kbx81/RGBBinaryClock/src/v1/Hardware.h

//
// kbx81's binary clock Hardware class
// ---------------------------------------------------------------------------
// (c)2017 by kbx81. See LICENSE for details.
//
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
#pragma once

#include <cstddef>
#include <cstdint>
#include "DateTime.h"
#include "Display.h"
#include "RgbLed.h"

#ifndef HARDWARE_VERSION
  #error HARDWARE_VERSION must be defined with a value between 1 and 4
#endif


namespace kbxBinaryClock {

namespace Hardware {

  /// @brief SPI1 peripherals
  ///
  enum SpiPeripheral : uint8_t {
    NotInitialized,
    LedDriversGs,
    LedDriversOther,
    Rtc,
    TempSensor
  };

  /// @brief Hardware request return codes
  ///
  enum HwReqAck : uint8_t {
    HwReqAckOk,
    HwReqAckBusy,
    HwReqAckError
  };


  /// @brief Hardware version to build for
  ///
  static const uint32_t cTargetHardwareVersion = HARDWARE_VERSION;


  /// @brief Initialize the hardware
  ///
  void     initialize();

  /// @brief Refreshes hardware external to the MCU
  ///
  void     refresh();

  /// @brief Generates a tick sound if no tone is active
  /// @return HwReqOk if tick was activated, HwReqBusy if tick was queued, else HwReqError
  HwReqAck tick();

  /// @brief Generates a tone of frequency for duration milliseconds
  /// @return HwReqOk if tone was activated, HwReqBusy if tone was queued, else HwReqError
  HwReqAck tone(const uint16_t frequency, const uint16_t duration);

  /// @brief Returns true if an external alarm input pin is active (they are active low)
  ///
  bool     alarmInput(const uint8_t alarmInputNumber);

  /// @brief Check a button
  ///
  bool     button(const uint8_t button);

  /// @brief Returns a bitmap indicating the state of all six buttons
  ///
  uint8_t  buttons();

  /// @brief Returns a bitmap indicating buttons that were pressed since the last check
  ///
  uint8_t  buttonsPressed();

  /// @brief Returns a bitmap indicating buttons that were released since the last check
  ///
  uint8_t  buttonsReleased();

  /// @brief Refreshes the button states from the TSC
  ///
  void     buttonsRefresh();

  /// @brief Set the current drive level for the drivers
  ///
  void     setLedCurrentDrive(const uint8_t drive);

  /// @brief Enable or disable the display blanking output pin
  ///
  void     setDisplayHardwareBlanking(const bool blankingState);

  /// @brief Returns the state of daylight savings time in hardware
  ///
  bool     dstState();

  /// @brief Get the current date/time
  ///
  DateTime getDateTime();

  /// @brief Set the date/time
  ///
  void     setDateTime(const DateTime &dateTime);

  /// @brief Returns the state of the RTC (true if year != 0)
  ///
  bool     rtcIsSet();

  /// @brief Returns the temperature based on hardware
  ///  (in fahrenheit if fahrenheit == true; in BCD if bcd == true)
  int32_t  temperature(const bool fahrenheit, const bool bcd);

  /// @brief Returns the level of light seen by the phototransistor (0 = min, 4095 = max)
  ///
  uint16_t lightLevel();

  /// @brief Adjusts the clock for daylight savings
  ///
  void     setDstState(const bool enableDst, const bool adjustRtcHardware);

  /// @brief Sets the value used as a threshold for flicker reduction at low intensities
  ///
  void     setFlickerReduction(const uint16_t value);

  /// @brief Sets the calibration value used for the temperature calculation
  ///
  void     setTemperatureCalibration(const int8_t value);

  /// @brief Sets the volume of tones emitted from the buzzer
  ///  Valid range is 0 (muted/minimum) to 7 (maximum/default)
  void     setVolume(const uint8_t volumeLevel);

  /// @brief Returns a CRC for the given data; expects 32-bit words
  ///
  uint32_t getCRC(uint32_t *inputData, uint32_t numElements);

  /// @brief Erases the FLASH area used for app data
  /// @return 0xff if startAddress is out of range, flash_get_status_flags() if
  ///  erase request failed, 0x40 if erase verification failed
  uint32_t eraseFlash(uint32_t startAddress);

  /// @brief Reads the FLASH area used for app data
  ///
  void     readFlash(uint32_t startAddress, uint16_t numElements, uint8_t *outputData);

  /// @brief Writes the FLASH area used for app data
  /// @return 0xff if startAddress is out of range, flash_get_status_flags() if
  ///  erase request failed, 0x40 if erase verification failed,
  ///  (0x80 | flash_get_status_flags()) if programming failure
  uint32_t writeFlash(uint32_t startAddress, uint8_t *inputData, uint16_t numElements);

  /// @brief Reads and/or writes data to/from specified I2C interface via DMA
  ///
  HwReqAck i2cTransfer(const uint8_t addr, const uint8_t *bufferTx, size_t numberTx, uint8_t *bufferRx, size_t numberRx);

  /// @brief Reads and/or writes data to/from the I2C1 interface via DMA
  ///
  HwReqAck i2cReceive(const uint8_t addr, uint8_t *bufferRx, const size_t numberRx, const bool autoEndXfer);
  HwReqAck i2cTransmit(const uint8_t addr, const uint8_t *bufferTx, const size_t numberTx, const bool autoEndXfer);

  /// @brief Aborts a transfer initiated by i2cTransfer()
  ///
  void     i2cAbort();

  /// @brief Permits checking the status of the I2C; returns true if busy
  ///
  bool     i2cIsBusy();

  /// @brief Reads data from the serial port with DMA
  /// @return false if failure (the USART was busy)
  HwReqAck readSerial(const uint32_t usart, const uint32_t length, char* data);

  /// @brief Writes data to the serial port with DMA
  /// @return false if failure (the USART was busy)
  HwReqAck writeSerial(const uint32_t usart, const uint32_t length, const char* data);

  /// @brief Transfers data in/out through the SPI via DMA
  /// @return false if failure (the SPI was busy)
  HwReqAck spiTransfer(const SpiPeripheral peripheral, uint8_t *bufferIn, uint8_t *bufferOut, const uint16_t length, const bool use16BitXfers);

  /// @brief Permits checking the status of the SPI; returns true if busy
  ///
  bool     spiIsBusy();

  /// @brief Sets the given status LED to the given intensity/RgbLed
  ///
  void     setBlueLed(const uint32_t intensity);
  void     setGreenLed(const uint32_t intensity);
  void     setRedLed(const uint32_t intensity);
  void     setStatusLed(const RgbLed led);
  void     blinkStatusLed(const RgbLed led1, const RgbLed led2, uint32_t numberOfBlinks, const uint32_t delayLength);

  /// @brief Creates a delay of length based on systick (configured for milliseconds)
  ///
  void     delay(const uint32_t length);

  /// @brief Converts to/from int/BCD
  /// @return encoded value
  ///
  uint32_t bcdToUint32(uint32_t bcdValue);
  uint32_t uint32ToBcd(uint32_t uint32Value); // beware of values > 99999999


  /// @brief Interrupt Service Routines
  ///
  void     dmaIsr();
  void     systickIsr();
  void     tim2Isr();
  void     tim15Isr();
  void     tim16Isr();
  void     tscIsr();
  void     usart1Isr();
  void     usart2Isr();

}

}
