kbx81/RGBBinaryClock/src/v1/Application.cpp

//
// kbx81's binary clock main application
// ---------------------------------------------------------------------------
// (c)2017 by kbx81. See LICENSE for details.
//
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
#include <cstdint>

#include "Application.h"
#include "AlarmHandler.h"
#include "DateTime.h"
#include "Display.h"
#include "DisplayManager.h"
#include "Dmx-512-Controller.h"
#include "Dmx-512-Rx.h"
#include "Dmx-512-View.h"
#include "Keys.h"
#include "Settings.h"
#include "MainMenuView.h"
#include "TestDisplayView.h"
#include "TimeDateTempView.h"
#include "TimerCounterView.h"
#include "SetTimeDateView.h"
#include "SetValueView.h"
#include "SetBitsView.h"
#include "SetColorsView.h"


// Workaround for  "hidden symbol `__dso_handle' isn't defined" linker error
void* __dso_handle;


namespace kbxBinaryClock {

namespace Application {


// An array with all views for the application
//
static View* const cModeViews[] = {
    new MainMenuView(),
    new TimeDateTempView(),
    new TimerCounterView(),
    new Dmx512View(),
    new SetTimeDateView(),
    new SetBitsView(),
    new SetValueView(),
    new SetColorsView(),
    new TestDisplayView()
};

// Structure defining menu views
//
struct viewDescriptor {
  uint8_t  menuItemDisplayNumber;
  ViewEnum view;
  uint8_t  relatedSettingNumber;
};


// An array of mode display numbers and their corresponding views
//
static viewDescriptor const cViewDescriptor[] = {
    {  0, ViewEnum::MainMenuViewEnum,     Settings::Setting::SystemOptions }, // OperatingModeMainMenu
    {  1, ViewEnum::TimeDateTempViewEnum, Settings::Setting::SystemOptions }, // OperatingModeFixedDisplay
    {  2, ViewEnum::TimeDateTempViewEnum, Settings::Setting::SystemOptions }, // OperatingModeToggleDisplay
    {  3, ViewEnum::TimerCounterViewEnum, Settings::Setting::SystemOptions }, // OperatingModeTimerCounter
    {  4, ViewEnum::Dmx512ViewEnum,       Settings::Setting::SystemOptions }, // OperatingModeDmx512Display
    {  5, ViewEnum::SetTimeDateViewEnum,  Settings::Setting::SystemOptions }, // OperatingModeSetClock
    {  6, ViewEnum::SetTimeDateViewEnum,  Settings::Setting::SystemOptions }, // OperatingModeSetDate
    {  7, ViewEnum::SetValueViewEnum,     Settings::Setting::TimerResetValue },
    { 10, ViewEnum::SetBitsViewEnum,      Settings::Setting::SystemOptions },
    { 11, ViewEnum::SetBitsViewEnum,      Settings::Setting::BeepStates },
    { 12, ViewEnum::SetBitsViewEnum,      Settings::Setting::BlinkStates },
    { 13, ViewEnum::SetBitsViewEnum,      Settings::Setting::ColorStates },
    { 20, ViewEnum::SetValueViewEnum,     Settings::Setting::TimeDisplayDuration },
    { 21, ViewEnum::SetValueViewEnum,     Settings::Setting::DateDisplayDuration },
    { 22, ViewEnum::SetValueViewEnum,     Settings::Setting::TemperatureDisplayDuration },
    { 23, ViewEnum::SetValueViewEnum,     Settings::Setting::FadeDuration },
    { 24, ViewEnum::SetValueViewEnum,     Settings::Setting::DstBeginMonth },
    { 25, ViewEnum::SetValueViewEnum,     Settings::Setting::DstBeginDowOrdinal },
    { 26, ViewEnum::SetValueViewEnum,     Settings::Setting::DstEndMonth },
    { 27, ViewEnum::SetValueViewEnum,     Settings::Setting::DstEndDowOrdinal },
    { 28, ViewEnum::SetValueViewEnum,     Settings::Setting::DstSwitchDayOfWeek },
    { 29, ViewEnum::SetValueViewEnum,     Settings::Setting::DstSwitchHour },
    { 30, ViewEnum::SetValueViewEnum,     Settings::Setting::MinimumIntensity },
    { 31, ViewEnum::SetValueViewEnum,     Settings::Setting::FlickerReduction },
    { 32, ViewEnum::SetValueViewEnum,     Settings::Setting::CurrentDrive },
    { 33, ViewEnum::SetValueViewEnum,     Settings::Setting::TemperatureCalibration },
    { 34, ViewEnum::SetValueViewEnum,     Settings::Setting::BeeperVolume },
    { 35, ViewEnum::SetValueViewEnum,     Settings::Setting::DateFormat },
    { 36, ViewEnum::SetValueViewEnum,     Settings::Setting::DisplayRefreshInterval },
    { 39, ViewEnum::SetValueViewEnum,     Settings::Setting::DmxAddress },
    { 40, ViewEnum::SetTimeDateViewEnum,  Settings::Slot::Slot1 },
    { 41, ViewEnum::SetTimeDateViewEnum,  Settings::Slot::Slot2 },
    { 42, ViewEnum::SetTimeDateViewEnum,  Settings::Slot::Slot3 },
    { 43, ViewEnum::SetTimeDateViewEnum,  Settings::Slot::Slot4 },
    { 44, ViewEnum::SetTimeDateViewEnum,  Settings::Slot::Slot5 },
    { 45, ViewEnum::SetTimeDateViewEnum,  Settings::Slot::Slot6 },
    { 46, ViewEnum::SetTimeDateViewEnum,  Settings::Slot::Slot7 },
    { 47, ViewEnum::SetTimeDateViewEnum,  Settings::Slot::Slot8 },
    { 50, ViewEnum::SetColorsViewEnum,    Settings::Slot::Slot1 },
    { 51, ViewEnum::SetColorsViewEnum,    Settings::Slot::Slot2 },
    { 52, ViewEnum::SetColorsViewEnum,    Settings::Slot::Slot3 },
    { 53, ViewEnum::SetColorsViewEnum,    Settings::Slot::Slot4 },
    { 54, ViewEnum::SetColorsViewEnum,    Settings::Slot::Slot5 },
    { 55, ViewEnum::SetColorsViewEnum,    Settings::Slot::Slot6 },
    { 56, ViewEnum::SetColorsViewEnum,    Settings::Slot::Slot7 },
    { 57, ViewEnum::SetColorsViewEnum,    Settings::Slot::Slot8 },
    { 58, ViewEnum::SetColorsViewEnum,    Settings::Slot::SlotDate },
    { 59, ViewEnum::SetColorsViewEnum,    Settings::Slot::SlotTemperature },
    { 60, ViewEnum::SetColorsViewEnum,    Settings::Slot::SlotTimer },
    { 61, ViewEnum::SetColorsViewEnum,    Settings::Slot::SlotMenu },
    { 62, ViewEnum::SetColorsViewEnum,    Settings::Slot::SlotSet },
    { 98, ViewEnum::TestDisplayEnum,      Settings::Setting::SystemOptions }
};

// The maximum idle time before the application switches back to the default view
//   Counter is incremented by tick()
static const uint16_t cMaximumIdleCount = 60000;

// A value by which we multiply the preference stored in the Settings
//
static const uint8_t cMinimumIntensityMultiplier = 10;

// Idle cycle counter
//
volatile static uint16_t _idleCounter = cMaximumIdleCount;

// minimum intensity
//   100 = 1%
static uint16_t _minimumIntensity = cMinimumIntensityMultiplier;

// master display intensity
//
static uint16_t _intensityPercentage = _minimumIntensity;

// important daylight savings dates & times
//
static DateTime _currentTime, _dstStart, _dstEnd;

// daylight savings state
//
static DstState _dstState;

// The current mode of the application
//
static OperatingMode _applicationMode;

// The application's current view mode
//
static ViewMode _viewMode;

// The application's current external control mode
//
static ExternalControl _externalControlMode = ExternalControl::NoActiveExtControlEnum;

// The application's current settings
//
static Settings _settings;

// The current displayed view of the application
//
// View *_currentView = cModeViews[static_cast<uint8_t>(OperatingMode::OperatingModeFixedDisplay)];
static View *_currentView = cModeViews[static_cast<uint8_t>(ViewEnum::TimeDateTempViewEnum)];

// determines if display intensity is adjusted in real-time
//
static bool _autoAdjustIntensities = false;

// DMX-512 signal status the last time we checked
//
static bool _previousDmxState = false;

// True if settings need to be written to FLASH
//
static bool _settingsModified = false;


void initialize()
{
  if (_settings.loadFromFlash() == false)
  {
    // blink to alert that settings could not be loaded
    Hardware::blinkStatusLed(Application::green, Application::orange, 12, 80);
    Hardware::delay(500);
    Hardware::setStatusLed(RgbLed());
  }

  _currentTime = Hardware::getDateTime();
  // Update DST start and end dates and times based on RTC
  isDst(_currentTime);

  AlarmHandler::initialize();

  Dmx512Controller::initialize();
  // setOperatingMode() will refreshSettings()
  if (_settings.getSetting(Settings::Setting::SystemOptions, Settings::SystemOptionsBits::StartupToToggle) == true)
  {
    setOperatingMode(OperatingMode::OperatingModeToggleDisplay);
  }
  else
  {
    setOperatingMode(OperatingMode::OperatingModeFixedDisplay);
  }
}


uint8_t getModeDisplayNumber(OperatingMode mode)
{
  return cViewDescriptor[static_cast<uint8_t>(mode)].menuItemDisplayNumber;
}


uint8_t getModeDisplayNumber(uint8_t mode)
{
  if (mode <= static_cast<uint8_t>(OperatingMode::OperatingModeTestDisplay))
  {
    return cViewDescriptor[mode].menuItemDisplayNumber;
  }
  return 0;
}


OperatingMode getOperatingMode()
{
  return _applicationMode;
}


void setOperatingMode(OperatingMode mode)
{
  if (_applicationMode != mode)
  {
    const uint16_t writeLedIntensity = 1024;
    // first, write settings to FLASH, if needed
    if ((mode != OperatingMode::OperatingModeMainMenu) &&
        (mode < static_cast<uint8_t>(OperatingMode::OperatingModeSetSystemOptions)) &&
        (_settingsModified == true))
    {
      if (_settings.saveToFlash() == 0)
      {
        _settingsModified = false;
        Hardware::setGreenLed(writeLedIntensity);
      }
      else
      {
        Hardware::setRedLed(writeLedIntensity);
      }
      DisplayManager::doubleBlink();
      Hardware::setStatusLed(RgbLed());
    }
    // ensure hardware is consistent with current settings
    refreshSettings();
    // set the new mode
    _applicationMode = mode;
    _viewMode = ViewMode::ViewMode0;
    _currentView = cModeViews[static_cast<uint8_t>(cViewDescriptor[static_cast<uint8_t>(mode)].view)];
    _currentView->enter();
    // if something kicks back to the main menu, make sure we wait a full cycle
    if (mode == OperatingMode::OperatingModeMainMenu)
    {
      _idleCounter = 0;
    }
    // this enables controller() immediately upon entering this mode
    else if (mode == OperatingMode::OperatingModeDmx512Display)
    {
      _idleCounter = cMaximumIdleCount;
    }
  }
}


ViewMode getViewMode()
{
  return _viewMode;
}


void setViewMode(ViewMode mode)
{
  if (_viewMode != mode)
  {
    _viewMode = mode;
  }
}


uint8_t getOperatingModeRelatedSetting(OperatingMode mode)
{
  return cViewDescriptor[static_cast<uint8_t>(mode)].relatedSettingNumber;
}


ExternalControl getExternalControlState()
{
  return _externalControlMode;
}


Settings getSettings()
{
  return _settings;
}


Settings* getSettingsPtr()
{
  return &_settings;
}


void refreshSettings()
{
  // Update hardware things
  Hardware::setFlickerReduction(_settings.getRawSetting(Settings::Setting::FlickerReduction));
  Hardware::setVolume(_settings.getRawSetting(Settings::Setting::BeeperVolume));
  Hardware::setLedCurrentDrive(_settings.getRawSetting(Settings::Setting::CurrentDrive));
  Hardware::setTemperatureCalibration((int8_t)(-(_settings.getRawSetting(Settings::Setting::TemperatureCalibration))));

  DisplayManager::setDisplayRefreshInterval(_settings.getRawSetting(Settings::Setting::DisplayRefreshInterval));
  DisplayManager::setDisplayBlanking(false);

  _minimumIntensity = _settings.getRawSetting(Settings::Setting::MinimumIntensity) * cMinimumIntensityMultiplier;
  setIntensityAutoAdjust(_settings.getSetting(Settings::Setting::SystemOptions, Settings::SystemOptionsBits::AutoAdjustIntensity), true);
}


void setSettings(Settings settings)
{
  _settings = settings;

  refreshSettings();

  _settingsModified = true;
}


// Handles DST date/time computation and setup
//
bool isDst(const DateTime &currentTime)
{
  uint8_t firstDay;

  if (_dstStart.year(false) != currentTime.year(false))
  {
    _dstState = DstState::Reset;
    firstDay = ((_settings.getRawSetting(Settings::Setting::DstBeginDowOrdinal) - 1) * 7) + 1;

    do
    {
      _dstStart.setDate(currentTime.year(false), _settings.getRawSetting(Settings::Setting::DstBeginMonth), firstDay++);
    }
    while((_dstStart.dayOfWeek() != _settings.getRawSetting(Settings::Setting::DstSwitchDayOfWeek)) && (firstDay <= 31));

    _dstStart.setTime(_settings.getRawSetting(Settings::Setting::DstSwitchHour), 0, 0);

    if (currentTime >= _dstStart)
    {
      _dstState = DstState::Spring;
    }
  }

  if (_dstEnd.year(false) != currentTime.year(false))
  {
    firstDay = ((_settings.getRawSetting(Settings::Setting::DstEndDowOrdinal) - 1) * 7) + 1;

    do
    {
      _dstEnd.setDate(currentTime.year(false), _settings.getRawSetting(Settings::Setting::DstEndMonth), firstDay++);
    }
    while((_dstEnd.dayOfWeek() != _settings.getRawSetting(Settings::Setting::DstSwitchDayOfWeek)) && (firstDay <= 31));

    _dstEnd.setTime(_settings.getRawSetting(Settings::Setting::DstSwitchHour), 0, 0);

    if (currentTime >= _dstEnd)
    {
      _dstState = DstState::Fall;
    }
  }

  // once everything is calculated above, it becomes this simple...
  return (currentTime >= _dstStart && currentTime < _dstEnd);
}


// Handles updating of the clock hardware for DST
//
void _refreshDst()
{
  _currentTime = Hardware::getDateTime();

  if ((_currentTime >= _dstEnd) && (_dstState == DstState::Spring))
  {
    _dstState = DstState::Fall;
    Hardware::setDstState(isDst(_currentTime), true);
  }

  if ((_currentTime >= _dstStart) && (_dstState == DstState::Reset))
  {
    _dstState = DstState::Spring;
    Hardware::setDstState(isDst(_currentTime), true);
  }
}


// Updates the "master" intensity for the display based on lightLevel()
//
void _updateIntensityPercentage(const bool quick = false)
{
  // determine the new value for _intensityPercentage
  uint16_t currentPercentage = (Hardware::lightLevel() * RgbLed::cLed100Percent) / Display::cLedMaxIntensity;

  // make sure the intensity does not go below the minimum level
  if (currentPercentage < _minimumIntensity)
  {
    currentPercentage = _minimumIntensity;
  }

  if (quick == true)
  {
    _intensityPercentage = currentPercentage;
  }
  else
  {
    if (currentPercentage > _intensityPercentage)
    {
     _intensityPercentage++;
    }
    else if (currentPercentage < _intensityPercentage)
    {
     _intensityPercentage--;
    }
  }
}


bool getIntensityAutoAdjust()
{
  return _autoAdjustIntensities;
}


void setIntensityAutoAdjust(const bool enable, const bool quickAdjust)
{
  if (_autoAdjustIntensities != enable)
  {
    _autoAdjustIntensities = enable;

    if ((enable == true) && (quickAdjust == true))
    {
      _updateIntensityPercentage(quickAdjust);
    }
  }
}


uint16_t getIntensity()
{
  return _intensityPercentage;
}


void setIntensity(const uint16_t intensity)
{
  _autoAdjustIntensities = false;

  if (intensity < RgbLed::cLed100Percent)
  {
    _intensityPercentage = intensity;
  }
  else
  {
    _intensityPercentage = RgbLed::cLed100Percent;
  }
}


void tick()
{
  if (_idleCounter <= cMaximumIdleCount)
  {
    _idleCounter++;
  }

  if (_autoAdjustIntensities == true)
  {
    _updateIntensityPercentage();
  }
}


// Here lies the main application loop
//
void loop()
{
  while(true)
  {
    // Refresh hardware data (date, time, temperature, etc.)
    Hardware::refresh();

    // Check up on DST and adjust the time if enabled based on settings
    if (_settings.getSetting(Settings::Setting::SystemOptions, Settings::SystemOptionsBits::DstEnable) == true)
    {
      _refreshDst();
    }
    // We control the master display intensity only if DMX-512 is NOT active
    if (_externalControlMode != ExternalControl::Dmx512ExtControlEnum)
    {
      DisplayManager::setMasterIntensity(_intensityPercentage);
    }

    // Check the buttons
    Keys::scanKeys();
    if (Keys::hasKeyPress())
    {
      // Get the key from the buffer and process it
      auto key = Keys::getKeyPress();
      // Reset the counter since there has been button/key activity
      _idleCounter = 0;
      // If an alarm is active and external control is not, send keypresses there
      if ((AlarmHandler::isAlarmActive())
       && (_externalControlMode == Application::ExternalControl::NoActiveExtControlEnum))
      {
        AlarmHandler::keyHandler(key);
      }
      else
      {
        if (_currentView->keyHandler(key) == true)
        {
          // The key did something, so make the tick sound
          Hardware::tick();
          // Take control back
          _externalControlMode = ExternalControl::NoActiveExtControlEnum;
          // Make sure the display is visible
          DisplayManager::setDisplayBlanking(false);
        }
      }
    }
    // Execute the loop block of the current view
    _currentView->loop();
    // We do not signal alarms if some external control is active
    if (_externalControlMode == Application::ExternalControl::NoActiveExtControlEnum)
    {
      // Process any necessary alarms
      AlarmHandler::loop();
    }

    // If the idle counter has maxed out, kick back to the appropriate display mode
    if (_idleCounter >= cMaximumIdleCount)
    {
      // If there is an active signal, update _externalControlMode
      if (Dmx512Rx::signalIsActive() == true)
      {
        _externalControlMode = ExternalControl::Dmx512ExtControlEnum;
      }
      // Kick back to the default display mode
      else if (_externalControlMode == ExternalControl::NoActiveExtControlEnum)
      {
        // Only change the display mode if it isn't already one of the time/date/temp modes
        if ((_applicationMode != OperatingMode::OperatingModeToggleDisplay) &&
            (_applicationMode != OperatingMode::OperatingModeFixedDisplay) &&
            (_applicationMode != OperatingMode::OperatingModeTimerCounter))
        {
          if (_settings.getSetting(Settings::Setting::SystemOptions, Settings::SystemOptionsBits::StartupToToggle) == true)
          {
            setOperatingMode(OperatingMode::OperatingModeToggleDisplay);
          }
          else
          {
            setOperatingMode(OperatingMode::OperatingModeFixedDisplay);
          }
        }
      }
    }

    if (_externalControlMode == ExternalControl::Dmx512ExtControlEnum)
    {
      // Allow the DMX-512 controller to do its thing
      Dmx512Controller::controller();
    }

    // Deal with changes in the DMX-512 signal state
    if (Dmx512Rx::signalIsActive() != _previousDmxState)
    {
      _previousDmxState = Dmx512Rx::signalIsActive();

      if (_previousDmxState == true)
      {
        _externalControlMode = ExternalControl::Dmx512ExtControlEnum;
      }
      else
      {
        _externalControlMode = ExternalControl::NoActiveExtControlEnum;
        AlarmHandler::clearAlarm();   // just in case...
      }
      // Setting this mode activates the view but also kicks us back to the menu if there is no signal
      setOperatingMode(OperatingMode::OperatingModeDmx512Display);
    }
  }
}


}

}
