kbx81/RGBBinaryClock/src/v1/MainMenuView.cpp

//
// kbx81's binary clock MainMenuView class
// ---------------------------------------------------------------------------
// (c)2017 by kbx81. See LICENSE for details.
//
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
#include "Application.h"
#include "DateTime.h"
#include "DisplayManager.h"
#include "MainMenuView.h"
#include "Settings.h"


namespace kbxBinaryClock {


MainMenuView::MainMenuView()
  : _selectedMode(0),
    _previousMode(0)
{
}


void MainMenuView::enter()
{
  // correct the mode if it's out of range
  if ((_selectedMode == 0) || (_selectedMode > Application::OperatingMode::OperatingModeSetColors))
  {
    _selectedMode = Application::OperatingMode::OperatingModeFixedDisplay;
  }
  // if the clock is not set, select the SetClock mode automagically
  if (Hardware::rtcIsSet() == false)
  {
    _selectedMode = Application::OperatingMode::OperatingModeSetClock;
  }
  // if the clock is set but not the date, select the SetDate mode automagically
  else if (Hardware::getDateTime().yearShort(false) == 0)
  {
    _selectedMode = Application::OperatingMode::OperatingModeSetDate;
  }

  DisplayManager::setStatusLedAutoRefreshing(false);
  // Make sure the status LEDs are off
  Hardware::setStatusLed(RgbLed());
}


bool MainMenuView::keyHandler(Keys::Key key)
{
  bool tick = true;

  if ((key == Keys::Key::A) &&
      (_selectedMode == static_cast<uint8_t>(Application::OperatingMode::OperatingModeTestDisplay) + 1))
  {
    Hardware::setStatusLed(Application::red);

    Hardware::eraseFlash(Settings::cSettingsFlashAddress);
    _selectedMode = 1;

    DisplayManager::doubleBlink();
    DisplayManager::doubleBlink();
    Hardware::setStatusLed(RgbLed());
  }

  if (key == Keys::Key::B)
  {
    Application::setOperatingMode(Application::OperatingMode::OperatingModeFixedDisplay);
  }

  if (key == Keys::Key::C)
  {
    Application::setOperatingMode(Application::OperatingMode::OperatingModeToggleDisplay);
  }

  if (key == Keys::Key::D)
  {
    if (--_selectedMode == 0)
    {
      _selectedMode = 1;

      tick = false;
    }
  }

  if (key == Keys::Key::U)
  {
    _selectedMode++;

    if (_selectedMode > static_cast<uint8_t>(Application::OperatingMode::OperatingModeTestDisplay) + 1)
    {
      _selectedMode = static_cast<uint8_t>(Application::OperatingMode::OperatingModeTestDisplay) + 1;

      tick = false;
    }
  }

  if (key == Keys::Key::E)
  {
    if (_selectedMode <= static_cast<uint8_t>(Application::OperatingMode::OperatingModeTestDisplay))
    {
      Application::setOperatingMode((Application::OperatingMode)_selectedMode);
    }
  }

  return tick;
}


void MainMenuView::loop()
{
  Settings *pSettings = Application::getSettingsPtr();
  uint32_t displayBitMask = Application::getModeDisplayNumber(_selectedMode);

  if (displayBitMask == 0)
  {
    // fix up the last "Erase FLASH" mode value
    displayBitMask = 99;
  }

  if (pSettings->getSetting(Settings::Setting::SystemOptions, Settings::SystemOptionsBits::DisplayBCD))
  {
    displayBitMask = Hardware::uint32ToBcd(static_cast<uint16_t>(displayBitMask));
  }

  Display bcDisp(pSettings->getColor(Settings::Color::Color0, Settings::Slot::SlotMenu), pSettings->getColor(Settings::Color::Color1, Settings::Slot::SlotMenu), displayBitMask << 16);

  DisplayManager::writeDisplay(bcDisp);
}


}
