kbx81/RGBBinaryClock/src/v1/RgbLed.cpp

//
// kbx81's RGB LED Library
// ---------------------------------------------------------------------------
// (c)2017 by kbx81. See LICENSE for details.
//
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

#include "RgbLed.h"

/// @mainpage
///
/// @section intro_sec Introduction
///
/// This library contains a class to manage the Binary Clock's RGB LEDs.
///
/// @section requirements_sec Requirements
///
/// This library is written in a manner so as to be compatible on a range of
/// CPUs/MCUs. It has been tested on Arduino and STM32F0 platforms. It requires
/// a modern C++ compiler (C++11).
///
/// @section classes_sec Classes
///
/// There is only the RgbLed::RgbLed class. Read the documentation of this class
/// for all details.
///


namespace kbxBinaryClock {


  /// 4096-step (12 bit) brightness table: gamma = 2.2
  ///
  const uint16_t RgbLed::cGammaTable[4096] = {
   0, 0, 0, 0, 0, 0, 0, 0, 0, 0, 0, 0, 0, 0, 0, 0, 0, 0, 0, 0, 0, 0, 0, 0, 0, 0, 0, 0, 0, 0, 0, 0, 0, 0, 0, 0, 0, 0, 0, 0, 0, 0, 0, 0, 0, 0, 0, 0, 0, 0, 0, 0, 0, 0, 0, 0, 0, 0, 0, 0, 0, 0, 0, 0, 0, 0, 0, 0, 1, 1, 1, 1, 1, 1, 1, 1, 1, 1, 1, 1, 1, 1, 1, 1, 1, 1, 1, 1, 1, 1, 1, 1, 1, 1, 1, 1, 1, 1, 1, 1, 1, 1, 1, 1, 1, 1, 1, 1, 1, 1, 1, 1, 1, 2, 2, 2, 2, 2, 2, 2, 2, 2, 2, 2, 2, 2, 2, 2, 2, 2, 2, 2, 2, 2, 2, 2, 2, 2, 2, 2, 2, 2, 3, 3, 3, 3, 3, 3, 3, 3, 3, 3, 3, 3, 3, 3, 3, 3, 3, 3, 3, 3, 3, 3, 3, 3, 4, 4, 4, 4, 4, 4, 4, 4, 4, 4, 4, 4, 4, 4, 4, 4, 4, 4, 4, 4, 5, 5, 5, 5, 5, 5, 5, 5, 5, 5, 5, 5, 5, 5, 5, 5, 5, 6, 6, 6, 6, 6, 6, 6, 6, 6, 6, 6, 6, 6, 6, 6, 6, 7, 7, 7, 7, 7, 7, 7, 7, 7, 7, 7, 7, 7, 7, 7, 8, 8, 8, 8, 8, 8, 8, 8, 8, 8, 8, 8, 8, 8, 9, 9, 9, 9, 9, 9, 9, 9, 9, 9, 9, 9, 10, 10, 10, 10, 10, 10, 10, 10, 10, 10, 10, 10, 11, 11, 11, 11, 11, 11, 11, 11, 11, 11, 11, 11, 12, 12, 12, 12, 12, 12, 12, 12, 12, 12, 12, 13, 13, 13, 13, 13, 13, 13, 13, 13, 13, 14, 14, 14, 14, 14, 14, 14, 14, 14, 14, 15, 15, 15, 15, 15, 15, 15, 15, 15, 15, 16, 16, 16, 16, 16, 16, 16, 16, 16, 17, 17, 17, 17, 17, 17, 17, 17, 17, 17, 18, 18, 18, 18, 18, 18, 18, 18, 19, 19, 19, 19, 19, 19, 19, 19, 19, 20, 20, 20, 20, 20, 20, 20, 20, 21, 21, 21, 21, 21, 21, 21, 21, 22, 22, 22, 22, 22, 22, 22, 22, 23, 23, 23, 23, 23, 23, 23, 23, 24, 24, 24, 24, 24, 24, 24, 25, 25, 25, 25, 25, 25, 25, 25, 26, 26, 26, 26, 26, 26, 26, 27, 27, 27, 27, 27, 27, 27, 28, 28, 28, 28, 28, 28, 28, 29, 29, 29, 29, 29, 29, 30, 30, 30, 30, 3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
9, 3951, 3953, 3956, 3958, 3960, 3962, 3964, 3966, 3968, 3971, 3973, 3975, 3977, 3979, 3981, 3984, 3986, 3988, 3990, 3992, 3994, 3997, 3999, 4001, 4003, 4005, 4008, 4010, 4012, 4014, 4016, 4018, 4021, 4023, 4025, 4027, 4029, 4031, 4034, 4036, 4038, 4040, 4042, 4045, 4047, 4049, 4051, 4053, 4056, 4058, 4060, 4062, 4064, 4066, 4069, 4071, 4073, 4075, 4077, 4080, 4082, 4084, 4086, 4088, 4091, 4093, 4095};


  RgbLed::RgbLed(const uint16_t red, const uint16_t green, const uint16_t blue, const uint32_t duration)
    : _red(red),
      _green(green),
      _blue(blue),
      _duration(duration)
  {
  }


  bool RgbLed::operator==(const RgbLed &other) const
  {
    return _red == other._red &&
            _green == other._green &&
            _blue == other._blue &&
            _duration == other._duration;
  }


  bool RgbLed::operator!=(const RgbLed &other) const
  {
    return _red != other._red ||
            _green != other._green ||
            _blue != other._blue ||
            _duration != other._duration;
  }


  void RgbLed::setRed(const uint16_t intensityRed)
  {
    _red = intensityRed;
  }


  void RgbLed::setGreen(const uint16_t intensityGreen)
  {
    _green = intensityGreen;
  }


  void RgbLed::setBlue(const uint16_t intensityBlue)
  {
    _blue = intensityBlue;
  }


  void RgbLed::setRGB(const uint16_t intensityRed, const uint16_t intensityGreen, const uint16_t intensityBlue)
  {
    _red = intensityRed;
    _green = intensityGreen;
    _blue = intensityBlue;
  }


  void RgbLed::setOff()
  {
    _red = 0;
    _green = 0;
    _blue = 0;
  }


  void RgbLed::setDuration(const uint32_t duration)
  {
    _duration = duration;
  }


  uint16_t RgbLed::getRed() const
  {
    return _red;
  }


  uint16_t RgbLed::getGreen() const
  {
    return _green;
  }


  uint16_t RgbLed::getBlue() const
  {
    return _blue;
  }


  uint32_t RgbLed::getDuration() const
  {
    return _duration;
  }


  void RgbLed::adjustIntensity(uint16_t percentageOfCurrentx100)
  {
    uint32_t top;

    if (percentageOfCurrentx100 > cLed100Percent)
    {
      percentageOfCurrentx100 = cLed100Percent;
    }

    top = _red * percentageOfCurrentx100;
    _red = top / cLed100Percent;

    top = _green * percentageOfCurrentx100;
    _green = top / cLed100Percent;

    top = _blue * percentageOfCurrentx100;
    _blue = top / cLed100Percent;
  }


  void RgbLed::mergeWithRgbLed(uint16_t percentageOfOriginalLedx100, const RgbLed &led)
  {
    int32_t intensity;

    if (percentageOfOriginalLedx100 > cLed100Percent)
    {
      percentageOfOriginalLedx100 = cLed100Percent;
    }

    // new intensity = led0 - ((led0 - led1) * percentage)
    intensity = _red - led.getRed();
    intensity = _red - ((intensity * percentageOfOriginalLedx100) / cLed100Percent);
    _red = intensity;

    intensity = _green - led.getGreen();
    intensity = _green - ((intensity * percentageOfOriginalLedx100) / cLed100Percent);
    _green = intensity;

    intensity = _blue - led.getBlue();
    intensity = _blue - ((intensity * percentageOfOriginalLedx100) / cLed100Percent);
    _blue = intensity;
  }


  void RgbLed::setFromMergedRgbLeds(uint16_t percentageOfLed0x100, const RgbLed &led0, const RgbLed &led1)
  {
    int32_t intensity;

    if (percentageOfLed0x100 > cLed100Percent)
    {
      percentageOfLed0x100 = cLed100Percent;
    }

    // new intensity = led0 - ((led0 - led1) * percentage)
    intensity = led0.getRed() - led1.getRed();
    intensity = led0.getRed() - ((intensity * percentageOfLed0x100) / cLed100Percent);
    _red = intensity;

    intensity = led0.getGreen() - led1.getGreen();
    intensity = led0.getGreen() - ((intensity * percentageOfLed0x100) / cLed100Percent);
    _green = intensity;

    intensity = led0.getBlue() - led1.getBlue();
    intensity = led0.getBlue() - ((intensity * percentageOfLed0x100) / cLed100Percent);
    _blue = intensity;
  }


  void RgbLed::gammaCorrect12bit()
  {
    const uint16_t mask = 0xfff;  // 12 bits

    _red = RgbLed::cGammaTable[_red & mask];
    _green = RgbLed::cGammaTable[_green & mask];
    _blue = RgbLed::cGammaTable[_blue & mask];
  }


}
