kbx81/RGBBinaryClock/src/v1/Application.h

//
// kbx81's binary clock main application
// ---------------------------------------------------------------------------
// (c)2017 by kbx81. See LICENSE for details.
//
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
#pragma once


#include <cstdint>

#include "Display.h"
#include "Settings.h"
#include "View.h"


namespace kbxBinaryClock {

namespace Application {

  /// @brief Application operating modes
  ///
  enum OperatingMode : uint8_t
  {
    OperatingModeMainMenu,            ///< Main Menu mode
    OperatingModeFixedDisplay,        ///< Fixed display mode
    OperatingModeToggleDisplay,       ///< Toggling display mode
    OperatingModeTimerCounter,        ///< Timer/counter mode
    OperatingModeDmx512Display,       ///< DMX-512 display mode
    OperatingModeSetClock,            ///< Set timeclock mode
    OperatingModeSetDate,             ///< Set date mode
    OperatingModeSetSystemOptions,    ///< Set Binary/BCD and 24 hour bits mode
    OperatingModeSlotBeepConfig,      ///< Enable/Disable beeping (alarm) per-slot
    OperatingModeSlotBlinkConfig,     ///< Enable/Disable display blinking per-slot
    OperatingModeSlotColorConfig,     ///< Enable/Disable color change per-slot
    OperatingModeSetDurationClock,    ///< Set duration of clock display mode
    OperatingModeSetDurationDate,     ///< Set duration of date display mode
    OperatingModeSetDurationTemp,     ///< Set duration of temperature display mode
    OperatingModeSetDurationFade,     ///< Set duration of fading for digits
    OperatingModeDstBeginMonth,       ///< Set first month of DST
    OperatingModeDstBeginDowOrdinal,  ///< Set which given day DST begins
    OperatingModeDstEndMonth,         ///< Set last month of DST
    OperatingModeDstEndDowOrdinal,    ///< Set which given day DST ends
    OperatingModeDstSwitchDayOfWeek,  ///< Set which day of week DST begins/ends
    OperatingModeDstSwitchHour,       ///< Set hour at which DST begins/ends
    OperatingModeSetMinimumIntensity, ///< Set minimum display intensity
    OperatingModeSetFlickerReduction, ///< Set flicker reduction value for display
    OperatingModeSetCurrentDrive,     ///< Set drive current for LEDs
    OperatingModeSetTempCalibration,  ///< Set temperature calibration
    OperatingModeSetBeeperVolume,     ///< Set Beeper Volume
    OperatingModeSetDateFormat,       ///< Set Date Format
    OperatingModeSetTimerResetValue,  ///< Set timer/counter reset value
    OperatingModeSetDisplayRefreshInterval, ///< Set display refresh interval
    OperatingModeSetDMX512Address,    ///< Set DMX-512 address mode
    OperatingModeSlot1Time,           ///< Set slot 1 time mode
    OperatingModeSlot2Time,           ///< Set slot 2 time mode
    OperatingModeSlot3Time,           ///< Set slot 3 time mode
    OperatingModeSlot4Time,           ///< Set slot 4 time mode
    OperatingModeSlot5Time,           ///< Set slot 5 time mode
    OperatingModeSlot6Time,           ///< Set slot 6 time mode
    OperatingModeSlot7Time,           ///< Set slot 7 time mode
    OperatingModeSlot8Time,           ///< Set slot 8 time mode
    OperatingModeSlot1Colors,         ///< Set slot 1 colors mode
    OperatingModeSlot2Colors,         ///< Set slot 2 colors mode
    OperatingModeSlot3Colors,         ///< Set slot 3 colors mode
    OperatingModeSlot4Colors,         ///< Set slot 4 colors mode
    OperatingModeSlot5Colors,         ///< Set slot 5 colors mode
    OperatingModeSlot6Colors,         ///< Set slot 6 colors mode
    OperatingModeSlot7Colors,         ///< Set slot 7 colors mode
    OperatingModeSlot8Colors,         ///< Set slot 8 colors mode
    OperatingModeDateColors,          ///< Set date colors mode
    OperatingModeTempColors,          ///< Set temperature colors mode
    OperatingModeTimerCounterColors,  ///< Set timer/counter colors mode
    OperatingModeMenuColors,          ///< Set menu colors mode
    OperatingModeSetColors,           ///< Set set colors mode
    OperatingModeTestDisplay          ///< Test display mode
  };

  /// @brief Enums for views
  ///
  enum ViewEnum : uint8_t
  {
      MainMenuViewEnum = 0,
      TimeDateTempViewEnum = 1,
      TimerCounterViewEnum = 2,
      Dmx512ViewEnum = 3,
      SetTimeDateViewEnum = 4,
      SetBitsViewEnum = 5,
      SetValueViewEnum = 6,
      SetColorsViewEnum = 7,
      TestDisplayEnum = 8
  };

  /// @brief Enums for views
  ///
  enum ExternalControl : uint8_t
  {
      NoActiveExtControlEnum,
      SerialExtControlEnum,
      Dmx512ExtControlEnum
  };

  /// @brief Enums for DST computation
  ///
  enum DstState : uint8_t
  {
    Reset,
    Spring,
    Fall
  };


  /// @brief Common colors used throughout
  ///
  static const RgbLed
    red(Display::cLedMaxIntensity, 0, 0),
    orange(Display::cLedMaxIntensity, Display::cLedMaxIntensity / 4, 0),
    yellow(Display::cLedMaxIntensity, Display::cLedMaxIntensity, 0),
    green(0, Display::cLedMaxIntensity, 0),
    cyan(0, Display::cLedMaxIntensity, Display::cLedMaxIntensity),
    blue(0, 0, Display::cLedMaxIntensity),
    violet(Display::cLedMaxIntensity / 8, 0, Display::cLedMaxIntensity),
    magenta(Display::cLedMaxIntensity, 0, Display::cLedMaxIntensity),
    white(Display::cLedMaxIntensity, Display::cLedMaxIntensity, Display::cLedMaxIntensity),
    gray(Display::cLedMaxIntensity / 8, Display::cLedMaxIntensity / 8, Display::cLedMaxIntensity / 8),
    darkGray(Display::cLedMaxIntensity / 24, Display::cLedMaxIntensity / 24, Display::cLedMaxIntensity / 24);

  /// @brief Initialize the application
  ///
  void initialize();

  /// @brief Get a mode's display number
  /// @param mode Desired mode to get the display number for
  ///
  uint8_t getModeDisplayNumber(OperatingMode mode);
  uint8_t getModeDisplayNumber(uint8_t mode);

  /// @brief Get application mode
  ///
  OperatingMode getOperatingMode();

  /// @brief Set new application mode
  /// @param mode New application mode
  ///
  void setOperatingMode(OperatingMode mode);

  /// @brief Get view mode
  ///
  ViewMode getViewMode();

  /// @brief Set new view mode
  /// @param mode New view mode
  ///
  void setViewMode(ViewMode mode);

  /// @brief Get view's related setting
  /// @param mode Desired mode to get the related setting for
  ///
  uint8_t getOperatingModeRelatedSetting(OperatingMode mode);

  /// @brief Get external control status
  ///
  ExternalControl getExternalControlState();

  /// @brief Get application settings
  ///
  Settings getSettings();
  Settings* getSettingsPtr();

  /// @brief Refreshes hardware from current application settings
  ///
  void refreshSettings();

  /// @brief Set new application settings, also calls refreshSettings()
  /// @param settings New settings to apply to the applications and hardware
  ///
  void setSettings(Settings settings);

  /// @brief Handles DST date/time computation; maintains clock's DST state machine.
  ///  Intended for tracking DST clock adjustments, not for arbitrary use!
  ///  To reset state machine, call with year != year provided when last called.
  /// @param currentTime DateTime object to compute DST state for
  /// @return true if DST is active based on passed DateTime object
  bool isDst(const DateTime &currentTime);

  /// @brief Returns state of automatic display intensity adjustments
  /// @return True if automatic intensity adjustment is enabled
  bool getIntensityAutoAdjust();

  /// @brief Enables/disables automagic adjusting of the display intensity based
  ///  on ambient light seen by the phototransistor
  /// @param enable Enables automatic adjustments if true
  /// @param quickAdjust Perform an immediate update of the intensity
  void setIntensityAutoAdjust(const bool enable, const bool quickAdjust = false);

  /// @brief Returns the application's current display intensity
  /// @return current display intensity percentage application is using (see RgbLed)
  uint16_t getIntensity();

  /// @brief Set the application's display intensity and disables automagic adjusting of the display intensity
  /// @param intensity New display intensity percentage application should use (see RgbLed)
  ///
  void setIntensity(const uint16_t intensity);

  /// @brief Refreshs master display intensity. Call at fixed intervals.
  ///
  void tick();

  /// @brief The main loop of the application.
  ///
  __attribute__((noreturn))
  void loop();
}

}
