kbx81/RGBBinaryClock/src/v1/TimerCounterView.cpp

//
// kbx81's binary clock timer/counter view class
// ---------------------------------------------------------------------------
// (c)2017 by kbx81. See LICENSE for details.
//
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

#include "AlarmHandler.h"
#include "Application.h"
#include "DisplayManager.h"
#include "Hardware.h"
#include "Settings.h"
#include "TimerCounterView.h"


namespace kbxBinaryClock {


// number of seconds in a day
//
const uint32_t TimerCounterView::cMaxBcdValue = 999999;


TimerCounterView::TimerCounterView()
  : _lastTime(0),
    _timerValue(0),
    _fadeDuration(0),
    _countUp(false),
    _alarmReady(false)
{
}


void TimerCounterView::enter()
{
  // we don't use the status LED, so turn it off in case it was left on
  DisplayManager::writeStatusLed(RgbLed());
}


bool TimerCounterView::keyHandler(Keys::Key key)
{
  Settings *pSettings = Application::getSettingsPtr();
  bool tick = true;

  if (key == Keys::Key::A)
  {
    if (_countUp == true)
    {
      Application::setViewMode(static_cast<ViewMode>(TimerMode::TimerRunUp));
    }
    else
    {
      Application::setViewMode(static_cast<ViewMode>(TimerMode::TimerRunDown));
    }

    _fadeDuration = pSettings->getRawSetting(Settings::Setting::FadeDuration);
  }

  if (key == Keys::Key::B)
  {
    Application::setViewMode(static_cast<ViewMode>(TimerMode::TimerStop));
  }

  if (key == Keys::Key::C)
  {
    Application::setViewMode(static_cast<ViewMode>(TimerMode::TimerReset));
  }

  if (key == Keys::Key::D)
  {
    if (static_cast<TimerMode>(Application::getViewMode()) == TimerMode::TimerStop)
    {
      _timerValue--;
      _fadeDuration = 0;
    }
    else
    {
      _countUp = false;
    }
  }

  if (key == Keys::Key::U)
  {
    if (static_cast<TimerMode>(Application::getViewMode()) == TimerMode::TimerStop)
    {
      _timerValue++;
      _fadeDuration = 0;
    }
    else
    {
      _countUp = true;
    }
  }

  if (key == Keys::Key::E)
  {
    Application::setOperatingMode(Application::OperatingMode::OperatingModeMainMenu);
  }

  return tick;
}


void TimerCounterView::loop()
{
  Application::ExternalControl externalControlState = Application::getExternalControlState();
  DateTime  currentTime = Hardware::getDateTime();
  Display   bcDisp;
  RgbLed    led[2];
  Settings *pSettings = Application::getSettingsPtr();
  Settings::Slot colorSlot = Settings::Slot::SlotDmx;
  TimerMode currentTimerMode = static_cast<TimerMode>(Application::getViewMode());
  uint32_t  secondsSinceMidnight = currentTime.secondsSinceMidnight(false);
  uint16_t  timerResetValue = pSettings->getRawSetting(Settings::Setting::TimerResetValue);
  bool      displayBcd = pSettings->getSetting(Settings::Setting::SystemOptions, Settings::SystemOptionsBits::DisplayBCD),
            setFadeDuration = false;

  // determine display colors
  if (externalControlState != Application::ExternalControl::Dmx512ExtControlEnum)
  {
    colorSlot = Settings::Slot::SlotTimer;
    setFadeDuration = true;
  }

  led[0] = pSettings->getColor(Settings::Color::Color0, colorSlot, setFadeDuration);
  led[1] = pSettings->getColor(Settings::Color::Color1, colorSlot, setFadeDuration);

  if ((currentTimerMode != TimerMode::TimerRunUp) && (currentTimerMode != TimerMode::TimerRunDown)
   && (externalControlState != Application::ExternalControl::Dmx512ExtControlEnum))
  {
    led[0].setDuration(0);
    led[1].setDuration(0);
  }

  bcDisp.setDisplayColor0(led[0]);
  bcDisp.setDisplayColor1(led[1]);

  // now determine the bitmask for the display
  if ((currentTimerMode != TimerMode::TimerStop) && (_lastTime != secondsSinceMidnight))
  {
    _lastTime = secondsSinceMidnight;

    switch (currentTimerMode)
    {
      case TimerMode::TimerRunUp:
      _timerValue++;
      break;

      case TimerMode::TimerRunDown:
      _timerValue--;
      break;

      case TimerMode::TimerReset:
      if (_countUp == true)
      {
        _timerValue = 0;
      }
      else
      {
        _timerValue = timerResetValue;
      }
      AlarmHandler::clearAlarm();   // in case of external control (DMX-512)
      Application::setViewMode(static_cast<ViewMode>(TimerMode::TimerStop));
      break;

      default:
      break;
    }
  }

  // alarm handling
  if (_countUp == true)
  {
    if ((_timerValue == timerResetValue) && (_alarmReady == true))
    {
      AlarmHandler::activateTimerCounterAlarm();
      _alarmReady = false;
      Application::setViewMode(static_cast<ViewMode>(TimerMode::TimerStop));
    }
    else if ((_timerValue != timerResetValue) && (_alarmReady == false))
    {
      _alarmReady = true;
    }
  }
  else
  {
    if ((_timerValue == 0) && (_alarmReady == true))
    {
      AlarmHandler::activateTimerCounterAlarm();
      _alarmReady = false;
      Application::setViewMode(static_cast<ViewMode>(TimerMode::TimerStop));
    }
    else if ((_timerValue != 0) && (_alarmReady == false))
    {
      _alarmReady = true;
    }
  }

  if ((displayBcd == true) && (_timerValue > cMaxBcdValue))
  {
    // we'll use what the timer value is closer to to determine what it
    //  should be reset to
    if (_timerValue < cMaxBcdValue * 8)
    {
      _timerValue = 0;
    }
    else
    {
      _timerValue = cMaxBcdValue;
    }
  }

  // display timer in BCD if settings say so
  if (displayBcd == true)
  {
    bcDisp.setDisplayFromBitmap(Hardware::uint32ToBcd(_timerValue));
  }
  else
  {
    bcDisp.setDisplayFromBitmap(_timerValue);
  }

  if (pSettings->getSetting(Settings::Setting::SystemOptions, Settings::SystemOptionsBits::MSBsOff) == true)
  {
    bcDisp.setMsbPixelsOff(displayBcd);
  }

  DisplayManager::writeDisplay(bcDisp);
}


}
