kbx81/RGBBinaryClock/src/v1/Display.cpp

//
// kbx81's binary clock Display Library
// ---------------------------------------------------------------------------
// (c)2017 by kbx81. See LICENSE for details.
//
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
#include "Display.h"

/// @mainpage
///
/// @section intro_sec Introduction
///
/// This library contains a class to manage the Binary Clock's RGB LED display.
///
/// @section requirements_sec Requirements
///
/// This library is written in a manner so as to be compatible on a range of
/// CPUs/MCUs. It has been tested on Arduino and STM32F0 platforms. It requires
/// a modern C++ compiler (C++11).
///
/// @section classes_sec Classes
///
/// There is only the Display::Display class. Read the documentation of this class
/// for all details.
///

namespace kbxBinaryClock {


Display::Display()
: _color0(0, 128, 0),
  _color1(128, 0, 0),
  _displayBitmap(0x000000),
  _displayBitmapMask(0xffffff)
{
  setDisplayFromBitmap(0);
}


Display::Display(const RgbLed &color0, const RgbLed &color1, const RgbLed *data)
: _color0(color0),
  _color1(color1),
  _displayBitmap(0x000000),
  _displayBitmapMask(0x000000)
{
  uint8_t i = 0;

  for (i = 0; i < cPixelCount; i++)
  {
    _display[i] = data[i];
  }
}


Display::Display(const RgbLed &color0, const RgbLed &color1, const uint32_t bitmap)
: _color0(color0),
  _color1(color1),
  _displayBitmap(bitmap),
  _displayBitmapMask(0xffffff)
{
  for (uint8_t i = 0; i < cPixelCount; i++)
  {
    if (((bitmap >> i) & 1) == 1)
    {
      _display[i] = color1;
    }
    else
    {
      _display[i] = color0;
    }
  }
}


Display::Display(const RgbLed &color0, const RgbLed &color1, const uint8_t byte2, const uint8_t byte1, const uint8_t byte0)
: _color0(color0),
  _color1(color1),
  _displayBitmap(byte0),
  _displayBitmapMask(0xffffff)
{
  _displayBitmap |= (((uint32_t)byte2 << 16 ) | ((uint32_t)byte1 << 8));

  for (uint8_t i = 0; i < cPixelCount; i++)
  {
    if (((_displayBitmap >> i) & 1) == 1)
    {
      _display[i] = color1;
    }
    else
    {
      _display[i] = color0;
    }
  }
}


bool Display::operator==(const Display &other) const
{
  for (uint8_t i = 0; i < Display::cPixelCount; i++)
  {
    if (_display[i] != other._display[i])
    {
      return false;
    }
  }

  return _color0 == other._color0 &&
          _color1 == other._color1 &&
          _displayBitmap == other._displayBitmap &&
          _displayBitmapMask == other._displayBitmapMask;
}


bool Display::operator!=(const Display &other) const
{
  for (uint8_t i = 0; i < Display::cPixelCount; i++)
  {
    if (_display[i] != other._display[i])
    {
      return true;
    }
  }

  return _color0 != other._color0 ||
          _color1 != other._color1 ||
          _displayBitmap != other._displayBitmap ||
          _displayBitmapMask != other._displayBitmapMask;
}


void Display::setDisplayColor0(const RgbLed &color)
{
  _color0 = color;
}


void Display::setDisplayColor1(const RgbLed &color)
{
  _color1 = color;
}


void Display::setDisplayFromRaw(const RgbLed *data)
{
  for (uint8_t i = 0; i < cPixelCount; i++)
  {
    _display[i] = data[i];
  }
  _displayBitmapMask = 0x000000;
}


void Display::setDisplayFromBitmap(const uint32_t bitmap)
{
  uint8_t i = 0;

  for (i = 0; i < cPixelCount; i++)
  {
    if (((bitmap >> i) & 1) == 1)
    {
      _display[i] = _color1;
    }
    else
    {
      _display[i] = _color0;
    }
  }
  _displayBitmap = bitmap;
  _displayBitmapMask = 0xffffff;
}


void Display::setDisplayFromBytes(const uint8_t byte2, const uint8_t byte1, const uint8_t byte0)
{
  uint8_t  i = 0;
  uint32_t bitmap = ((uint32_t)byte2 << 16 ) | ((uint32_t)byte1 << 8) | (uint32_t)byte0;

  for (i = 0; i < cPixelCount; i++)
  {
    if (((bitmap >> i) & 1) == 1)
    {
      _display[i] = _color1;
    }
    else
    {
      _display[i] = _color0;
    }
  }
  _displayBitmap = bitmap;
  _displayBitmapMask = 0xffffff;
}


void Display::setDisplayFromNibbles(const uint8_t byte5, const uint8_t byte4, const uint8_t byte3, const uint8_t byte2, const uint8_t byte1, const uint8_t byte0)
{
  uint8_t  i = 0;
  uint32_t bitmap = (((uint32_t)byte5 & 0x0f) << 20)
                  | (((uint32_t)byte4 & 0x0f) << 16)
                  | (((uint32_t)byte3 & 0x0f) << 12)
                  | (((uint32_t)byte2 & 0x0f) << 8)
                  | (((uint32_t)byte1 & 0x0f) << 4 )
                  | ((uint32_t)byte0 & 0x0f);

  for (i = 0; i < cPixelCount; i++)
  {
    if (((bitmap >> i) & 1) == 1)
    {
      _display[i] = _color1;
    }
    else
    {
      _display[i] = _color0;
    }
  }
  _displayBitmap = bitmap;
  _displayBitmapMask = 0xffffff;
}


void Display::setPixelFromState(const uint8_t pixelNumber, const bool ledState)
{
  // set the pixel from the appropriate color "state"
  if (pixelNumber < cPixelCount)
  {
    if (ledState == true)
    {
      _display[pixelNumber] = _color1;
    }
    else
    {
      _display[pixelNumber] = _color0;
    }
  }
  // update bitmap
  if ((_displayBitmap & (1 << pixelNumber)) != 0)
  {
    _displayBitmap |= (1 << pixelNumber);
  }
  else
  {
    _displayBitmap &= ~(1 << pixelNumber);
  }
  // update bitmask
  _displayBitmapMask |= (1 << pixelNumber);
}


void Display::setPixelFromRaw(const uint8_t pixelNumber, const RgbLed &color)
{
  if (pixelNumber < cPixelCount)
  {
    _display[pixelNumber] = color;
  }
  // update bitmask
  _displayBitmapMask &= ~(1 << pixelNumber);
}


void Display::setPixelOff(const uint8_t pixelNumber)
{
  if (pixelNumber < cPixelCount)
  {
    _display[pixelNumber].setOff();
  }
  // update bitmask
  _displayBitmapMask &= ~(1 << pixelNumber);
}


void Display::setPixelsOff(const uint32_t bitmap)
{
  for (uint8_t i = 0; (i < cPixelCount) && ((bitmap >> i) != 0); i++)
  {
    if (((bitmap >> i) & 1) == 1)
    {
      setPixelOff(i);
    }
  }
}


void Display::setMsbPixelsOff(const bool useBcdMode, const uint32_t keepOnMask)
{
  const uint32_t fullMask = 0xffffffff;
  uint32_t msbMask = 0;
  uint8_t  i, currentByte = 0, blockMask = 0xff, passes = 3, width = 8;

  if (useBcdMode == true)
  {
    blockMask = 0xf;
    passes = 6;
    width  = 4;
  }

  for (i = 0; i < passes; i++)
  {
    currentByte = (_displayBitmap >> (width * i)) & blockMask;

    msbMask |= (fullMask >> (__builtin_clz(currentByte))) << (width * i);
  }

  setPixelsOff((~msbMask) & keepOnMask);
}


bool Display::getPixelState(const uint8_t pixelNumber) const
{
  if (pixelNumber < cPixelCount)
  {
    if ((_displayBitmap & (1 << pixelNumber)) != 0)
    {
      return true;
    }
    else
    {
      return false;
    }
  }
  else
  {
    return false;
  }
}


bool Display::getPixelMask(const uint8_t pixelNumber) const
{
  if (pixelNumber < cPixelCount)
  {
    if ((_displayBitmapMask & (1 << pixelNumber)) != 0)
    {
      return true;
    }
    else
    {
      return false;
    }
  }
  else
  {
    return false;
  }
}


RgbLed Display::getPixelRaw(const uint8_t pixelNumber) const
{
  if (pixelNumber < cPixelCount)
  {
    RgbLed someRgbLed(_display[pixelNumber]);

    return someRgbLed;
  }
  return 0;
}


};
