kbx81/RGBBinaryClock/src/v1/DisplayManager.h

//
// kbx81's binary clock DisplayManager Library
// ---------------------------------------------------------------------------
// (c)2017 by kbx81. See LICENSE for details.
//
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
#pragma once


#include <cstdint>

#include "Display.h"
#include "RgbLed.h"


namespace kbxBinaryClock {

/// @brief kbx Binary Clock DisplayManager
///

namespace DisplayManager
{
  /// @brief Initialize DisplayManager
  ///
  void initialize();

  /// @brief Refreshes drivers and intensities of LEDs that are changing intensity levels due to (an) active crossfade(s)
  ///
  void refresh();

  /// @brief Triggers a refresh of LED intensities next time refresh() is called
  ///
  void tick();

  /// @brief Enables/Disables control of the status LED by refresh() (above)
  /// @param autoRefreshEnabled New state for status LED auto-refreshing
  ///
  void setStatusLedAutoRefreshing(const bool autoRefreshEnabled);

  /// @brief Returns the current "master" intensities of the display
  /// @return Current master intensity
  ///
  uint16_t getMasterIntensity();

  /// @brief Sets the "master" intensity of the display, where 10000 = 100%.
  ///   Values are gamma-corrected.
  /// @param intensity New master intensity for display. Display is updated at next refresh()
  void setMasterIntensity(const uint16_t intensity);

  /// @brief Get the state of display blanking
  /// @return true if display is blank/off
  ///
  bool getDisplayBlanking();

  /// @brief Blank the display
  /// @param blank Display is blank (off) if true
  ///
  void setDisplayBlanking(const bool blank);

  /// @brief Gets the interval used for refreshing the LED driver registers
  /// @return interval at which refresh occurs; based on systick
  ///
  uint8_t getDisplayRefreshInterval();

  /// @brief Set the interval for refreshing the LED driver registers
  /// @param interval Interval at which refresh occurs; based on systick
  ///
  void setDisplayRefreshInterval(const uint8_t interval);

  /// @brief Set the dot correction range used by the LED drivers
  /// @param useUpperRange Drivers will use the upper (33% to 100%) range if true
  ///
  void setDotCorrectionRange(const bool useUpperRange);

  /// @brief Set the dot correction value for a single LED
  /// @param ledNumber LED number to adjust
  /// @param value Adjustment level for given LED (7 bits)
  ///
  void setDotCorrectionValue(const uint8_t ledNumber, const uint8_t value);

  /// @brief Causes the display to blink twice (acknowledgement of some action)
  ///
  void doubleBlink();

  /// @brief Writes the passed display into the display buffer. LEDs will fade to the
  ///  intensities in the new display at the specified rates.
  /// @param display Display to be written
  /// @param statusLed Status LED state
  ///
  void writeDisplay(const Display &display);
  void writeDisplay(const Display &display, const RgbLed &statusLed);

  /// @brief Sets the status LED's state
  /// @param statusLed New status LED state
  ///
  void writeStatusLed(const RgbLed &statusLed);


}


}
