kbx81/RGBBinaryClock/src/v1/RgbCrossfader.h

//
// kbx81's binary clock RgbCrossfader Library
// ---------------------------------------------------------------------------
// (c)2017 by kbx81. See LICENSE for details.
//
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
#pragma once


#include <cstdint>

#include "RgbLed.h"


namespace kbxBinaryClock {

/// @brief kbx Binary Clock RgbCrossfader class
///

class RgbCrossfader
{
public:
  /// @brief Default constructor
  ///
  RgbCrossfader();

  /// @brief Returns true if a crossfade is in progress
  ///
  /// @return true if a crosfade is currently in progress/not complete
  ///
  bool fadeIsActive();

  /// @brief Gets the fader's active/current value
  ///
  /// @return fader's current values with duration set to number of ticks elapsed
  ///
  RgbLed getActive() const;

  /// @brief Gets the fader's target values
  ///
  /// @return fader's target values, fade duration included
  ///
  RgbLed getTargetWithDuration() const;

  /// @brief Restarts fade to target from active values with existing duration
  ///
  void resetFade();

  /// @brief Starts a new fade with (a) new target value(s)
  ///
  /// @param newTarget New RGB target values for fader, including duration
  ///
  void startNewFade(const RgbLed &newTarget);

  /// @brief Starts a new fade with (a) new target value(s) if target values are different from existing values
  ///
  /// @param newTarget New RGB target values for fader, including duration
  ///
  void startNewFadeIfDifferent(const RgbLed &newTarget);

  /// @brief Advances all crossfades currently in progress (call at fixed intervals)
  ///
  void tick();

  /// @brief Updates fade duration only
  ///
  /// @param newDuration New duration for fader (RgbLed RGB values ignored)
  ///
  void updateFadeDuration(const uint32_t newDuration);
  void updateFadeDuration(const RgbLed &newDuration);

  /// @brief Updates fade target value(s) only (resumes fade if it was completed)
  ///
  /// @param newTarget New target value(s) for fader
  /// @param startNewFade New fade begins if true
  ///
  void updateFadeTarget(const RgbLed &newTarget, const bool startNewFade = false);

  /// @brief Updates fade target value(s) and duration (resumes fade if it was completed)
  ///
  /// @param newTarget New target value(s) for fader including duration
  /// @param startNewFade New fade begins if true
  ///
  void updateFadeTargetAndDuration(const RgbLed &newTarget, const bool startNewFade = false);


private:
  RgbLed _active;   ///< current values of fader, duration value = tick counter
  RgbLed _start;    ///< values at which fade started, duration value unused
  RgbLed _target;   ///< target values for fader, duration value = duration of crossfade
};


}
