kbx81/RGBBinaryClock/src/v1/DS3234.h

//
// kbx81's binary clock DS3234 RTC class
// ---------------------------------------------------------------------------
// (c)2017 by kbx81. See LICENSE for details.
//
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
#pragma once

#include <cstdint>
#include "DateTime.h"
#include "Hardware.h"


namespace kbxBinaryClock {

namespace DS3234 {

// Library usage:
// 1. Set base year if required. Default is 2000.
// 2. Call isConnected() to determine if IC is available for use.
// 3. Call isValid() to determine validity of RTC data.
// 4. Call setDateTime() if required to set date & time.
// 5. Call refresh() to refresh register states from IC.
// 6. Call getDateTime() as required, typically after calling refresh().

// Configure the real time clock driver with a new base year
//
// @param yearBase The year base which is used for the RTC.
//    The RTC stores the year only with two digits, plus one
//    additional bit for the next century. If you set the
//    year base to 2000, the RTC will hold the correct time
//    for 200 years, starting from 2000-01-01 00:00:00.
//
void setBaseYear(uint16_t yearBase = 2000);

// Get the current date/time
//
DateTime getDateTime();

// Set the date/time
//
// @param dateTime The date and time to set in the RTC
void setDateTime(const DateTime &dateTime);

// Check if the RTC is connected; returns true if so
//
bool isConnected();

// Check if the RTC is running; returns true if so
//
bool isRunning();

// Check if the RTC is valid; returns true if so
//
bool isValid();

// Get the raw temperature register value
//
uint16_t getTemperatureRegister();

// Get the whole-number part of the temperature register (in degrees celsius)
//
int16_t getTemperatureWholePart();

// Get the fractional part of the temperature register (in degrees celsius)
//
uint16_t getTemperatureFractionalPart();

// Read all registers from the DS3234
//  Returns result of read from Hardware::spiTransfer
Hardware::HwReqAck refresh();

}

}
